fbarquez/pulsoxi_iot/images/Anexos/BPW34_Komponente.png

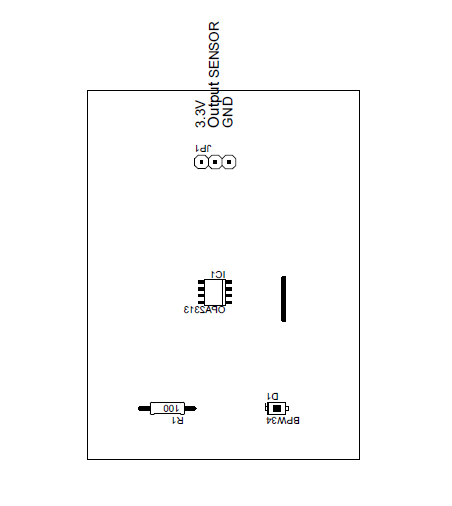
images/Anexos/BPW34_Komponente.png
