fbarquez/pulsoxi_iot/images/Anexos/BPW34_squema.png

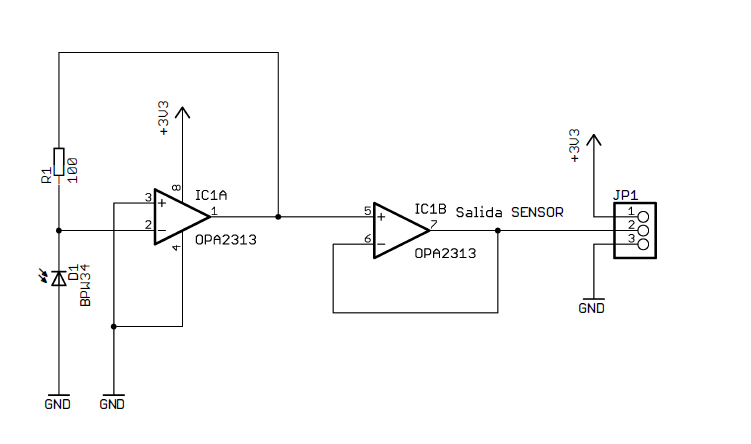
images/Anexos/BPW34_squema.png
