fbarquez/pulsoxi_iot/images/Anexos/IMG-20240221-WA0002.jpg

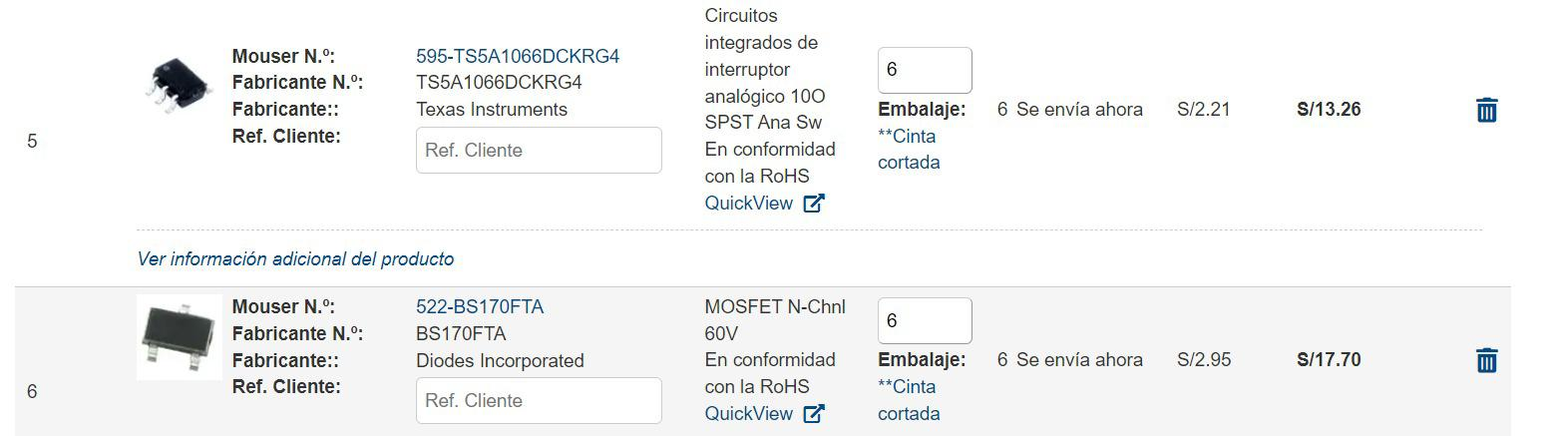
images/Anexos/IMG-20240221-WA0002.jpg
