fbarquez/pulsoxi_iot/images/Anexos/IMG-20240221-WA0005.jpg

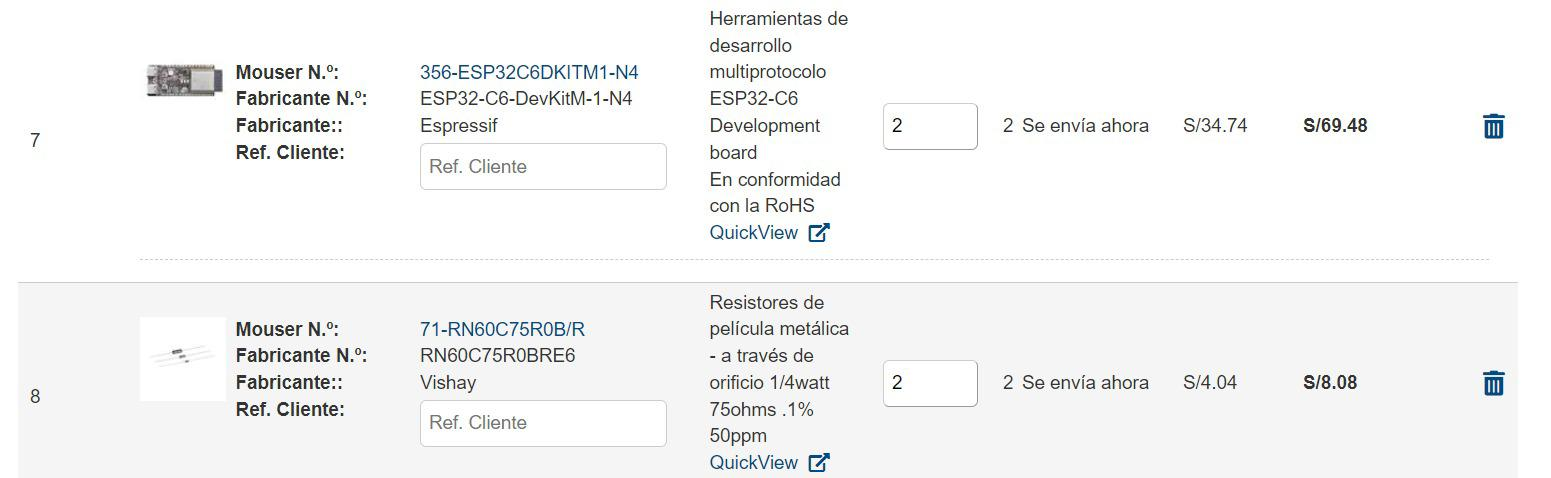
images/Anexos/IMG-20240221-WA0005.jpg
