fbarquez/pulsoxi_iot/images/Calculo Filtro pasabajos_y_filtro pasaaltos.png

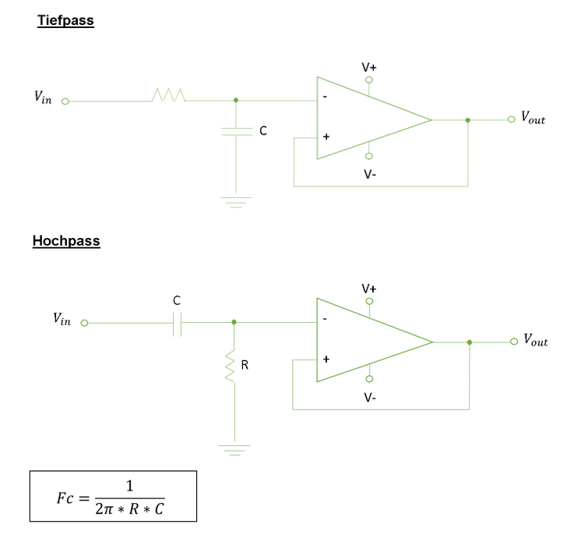
images/Calculo Filtro pasabajos_y_filtro pasaaltos.png
