fbarquez/pulsoxi_iot/images/Conexion_PIC16F1937_aESP32.jpg

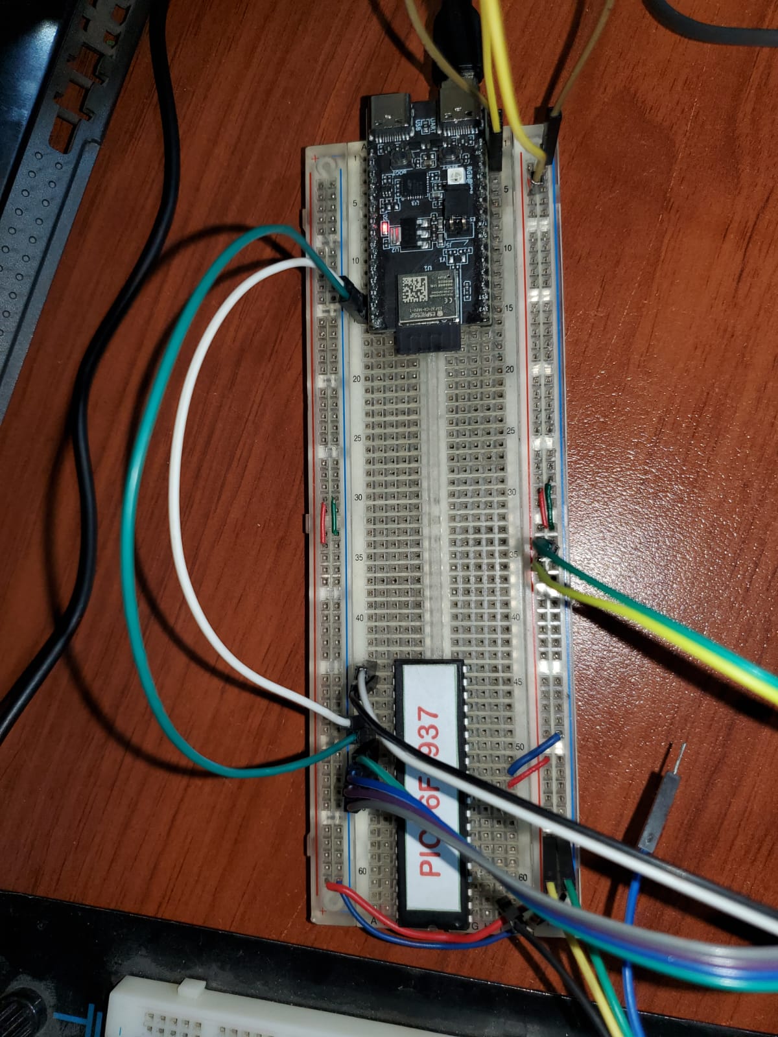
images/Conexion_PIC16F1937_aESP32.jpg
