fbarquez/pulsoxi_iot/images/Conexión PIC16F1937[6] misma Conexión.jpg

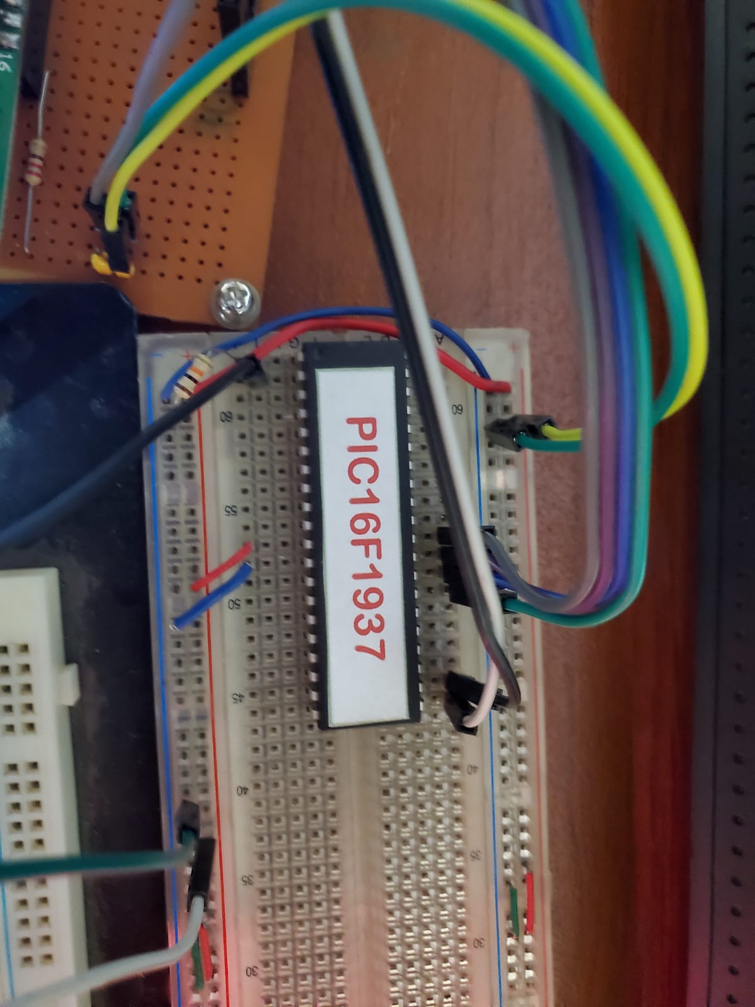
images/Conexión PIC16F1937[6] misma Conexión.jpg
