fbarquez/pulsoxi_iot/images/Cálculo amplificador no inversor.png

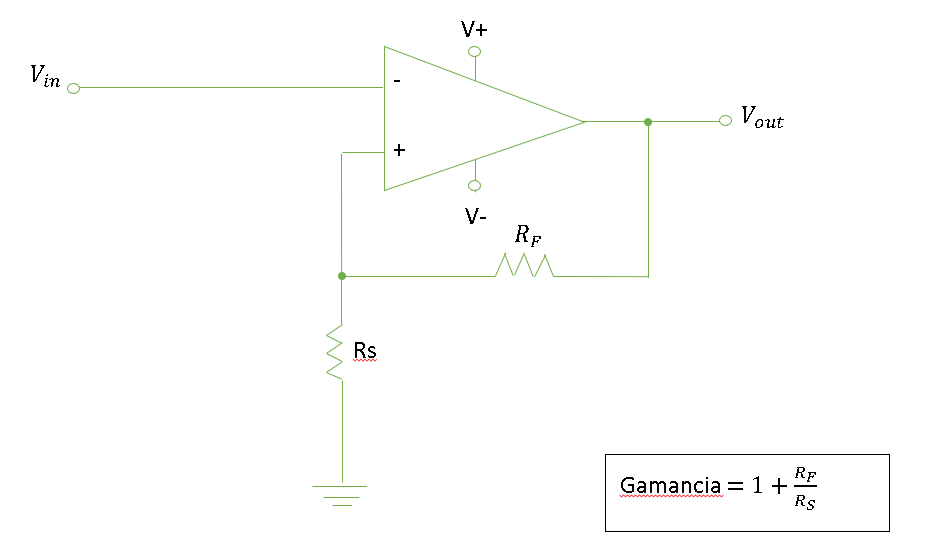
images/Cálculo amplificador no inversor.png
