fbarquez/pulsoxi_iot/images/Cálculo Conversor de corriente a Voltaje.png

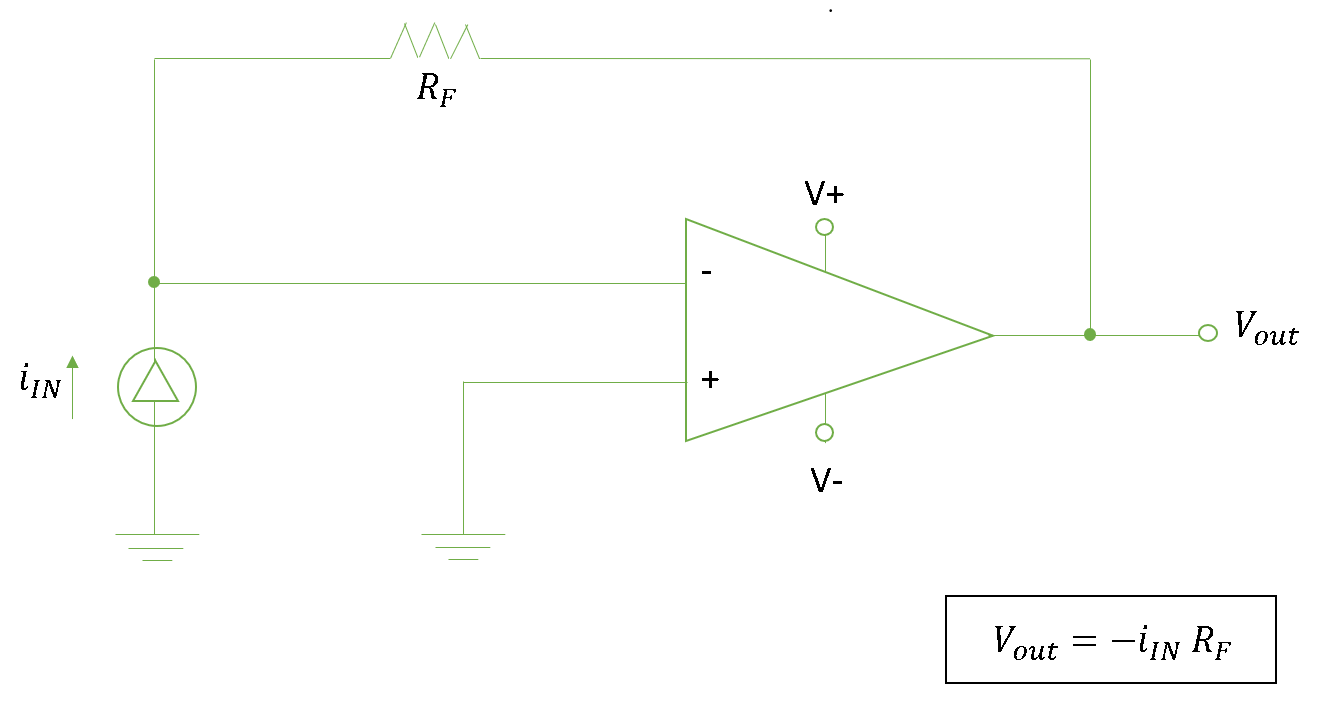
images/Cálculo Conversor de corriente a Voltaje.png
