fbarquez/pulsoxi_iot/images/DiagramadeConexion_SenhalesacondicionadasamicrocontroladoresPICyESP32.jpg

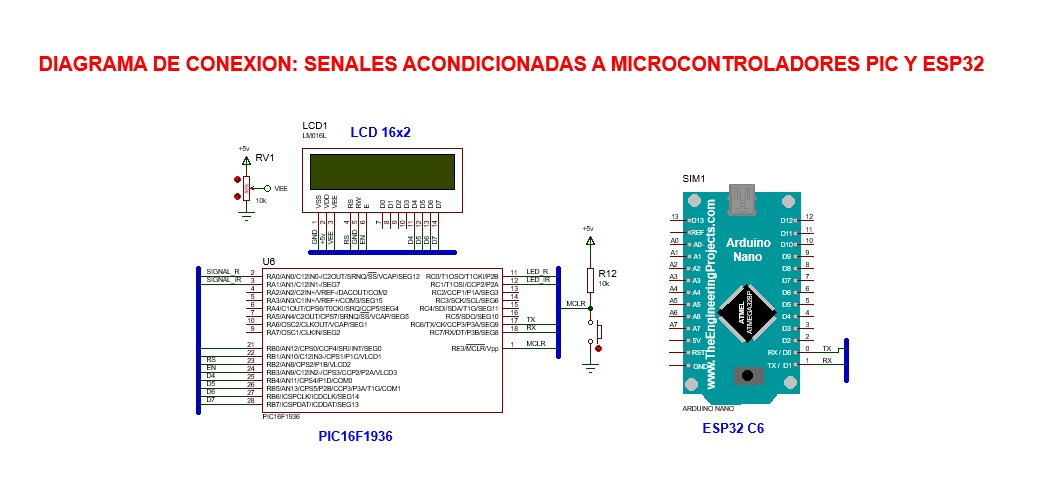
images/DiagramadeConexion_SenhalesacondicionadasamicrocontroladoresPICyESP32.jpg
