fbarquez/pulsoxi_iot/images/DiagramadeflujoparaelESP32.jpg

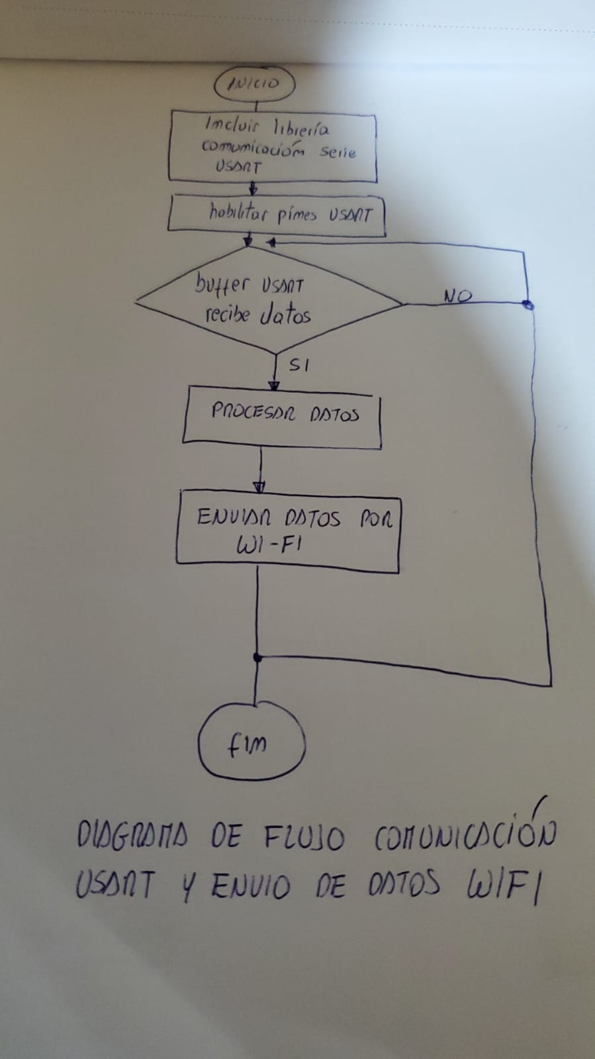
images/DiagramadeflujoparaelESP32.jpg
