fbarquez/pulsoxi_iot/images/Eagle/Board_Pulsoximeter.png

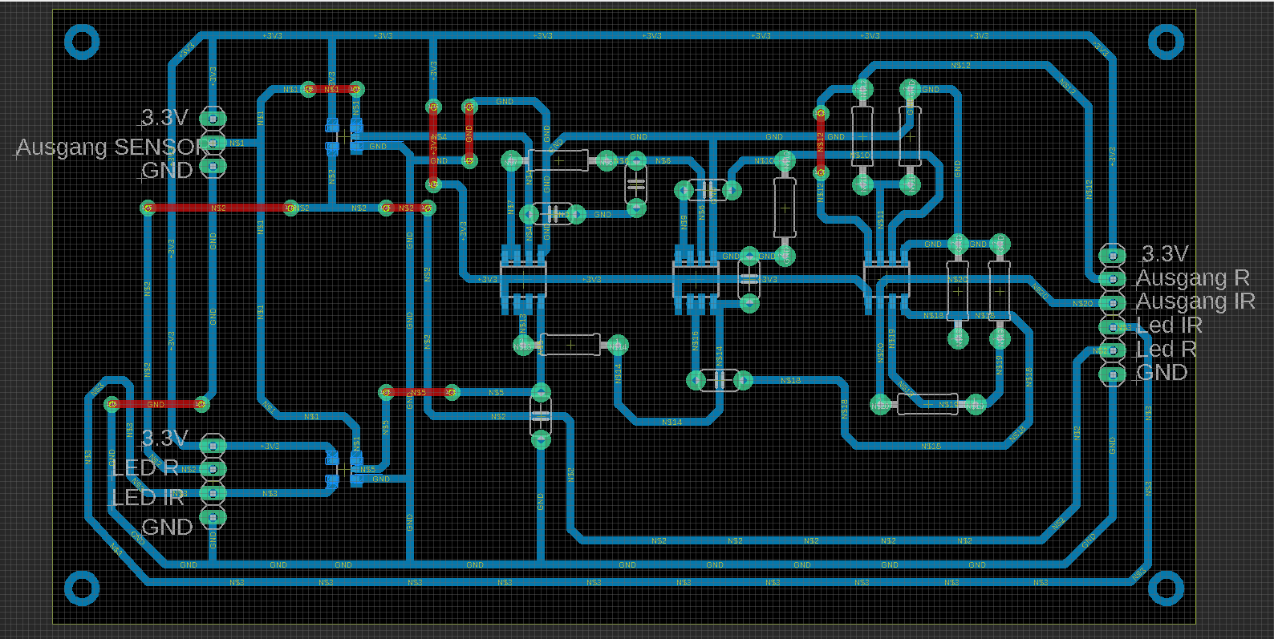
images/Eagle/Board_Pulsoximeter.png
