fbarquez/pulsoxi_iot/images/Eagle/Pulsioximeter_PCB_BottomSide.png

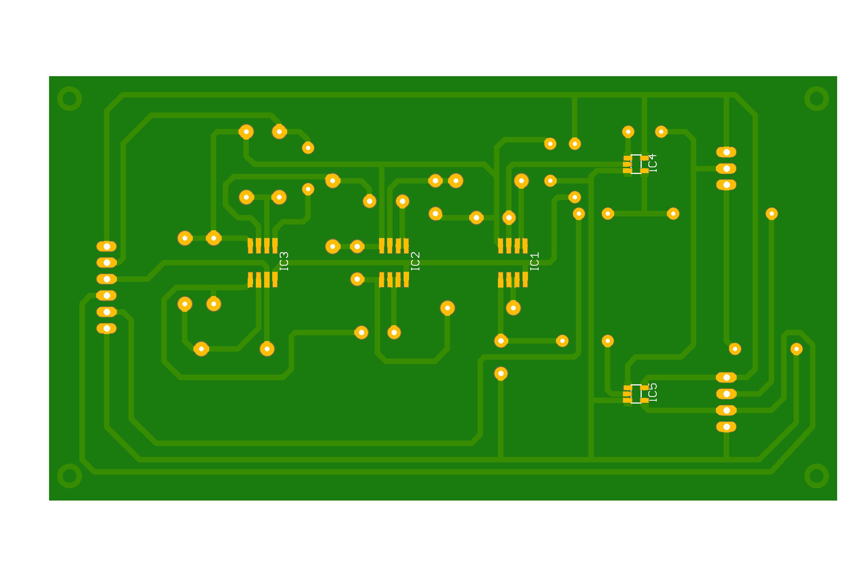
images/Eagle/Pulsioximeter_PCB_BottomSide.png
