fbarquez/pulsoxi_iot/images/Eagle/Pulsioximeter_PCB_TopSide.png

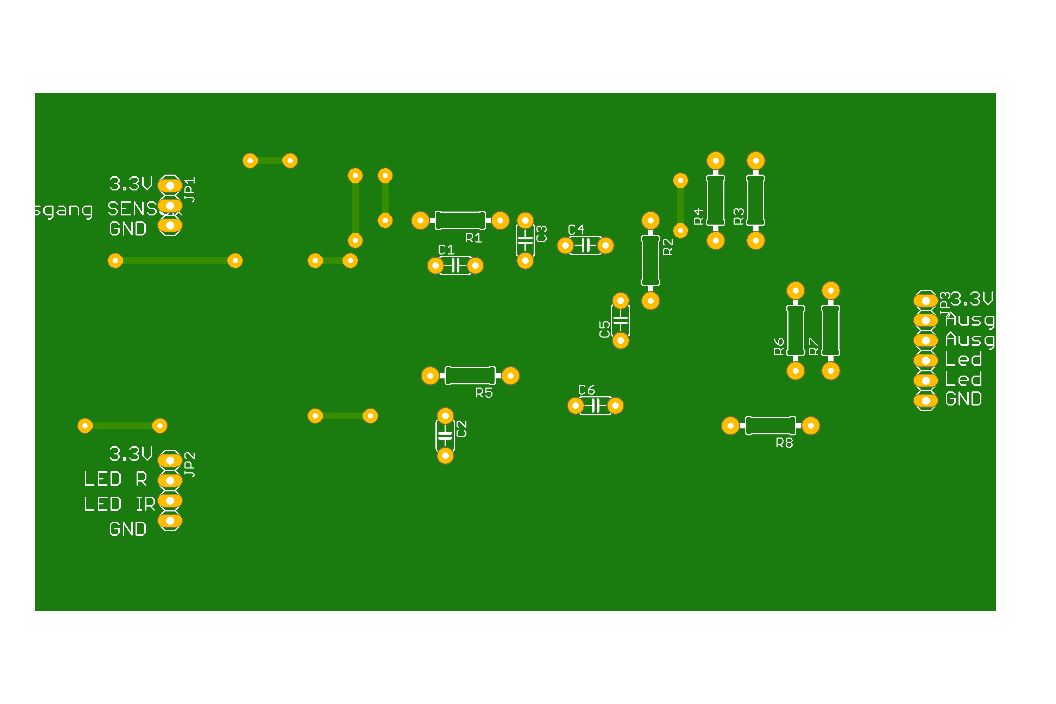
images/Eagle/Pulsioximeter_PCB_TopSide.png
