fbarquez/pulsoxi_iot/images/Eagle/Pulsioximetro_PCB_Drills.png

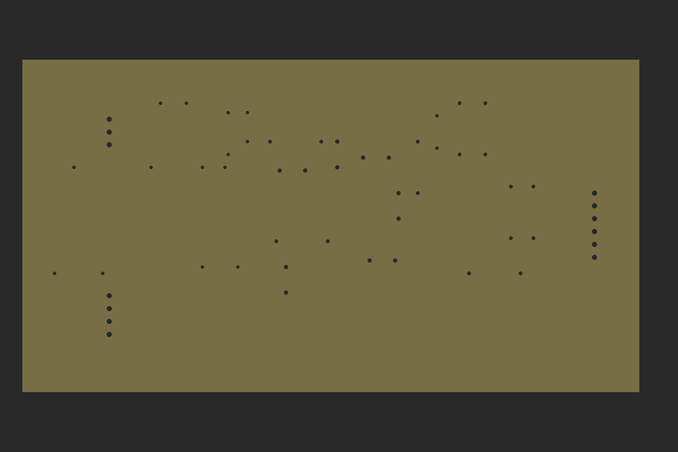
images/Eagle/Pulsioximetro_PCB_Drills.png
