fbarquez/pulsoxi_iot/images/Eagle/Schaltplan_BPW34.png

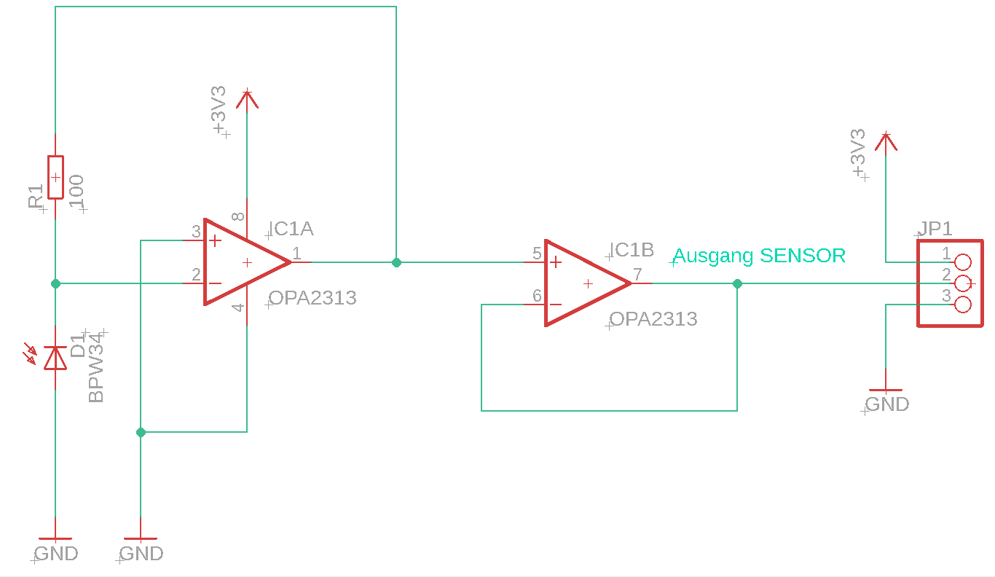
images/Eagle/Schaltplan_BPW34.png
