fbarquez/pulsoxi_iot/images/Eagle/Schaltplan_BS170.png

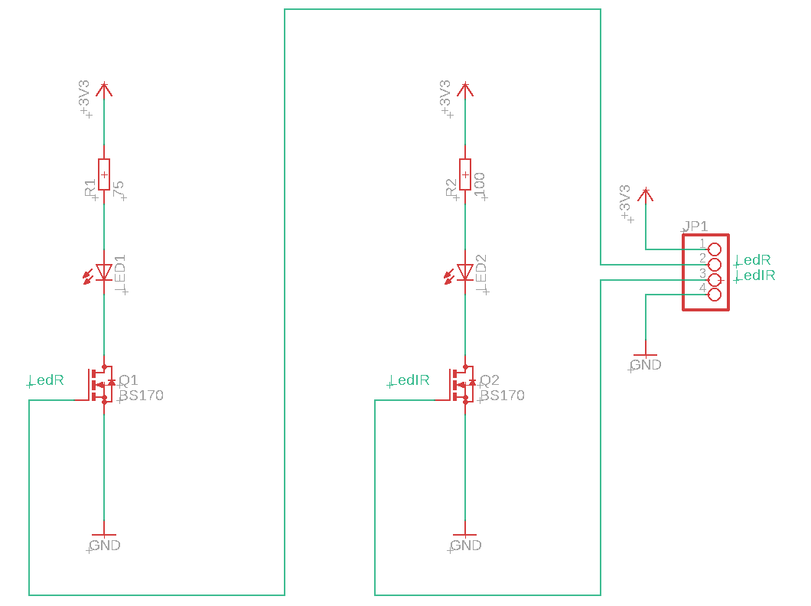
images/Eagle/Schaltplan_BS170.png
