fbarquez/pulsoxi_iot/images/Eagle/Schaltplan_Pulsoximeter.png

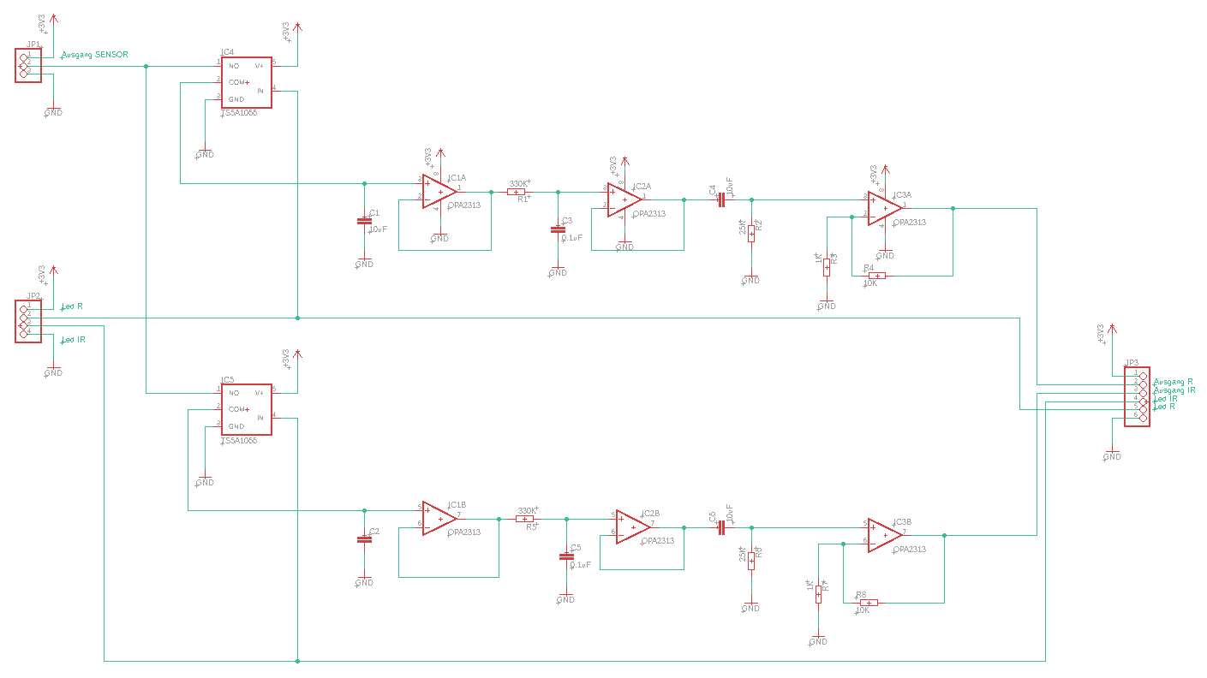
images/Eagle/Schaltplan_Pulsoximeter.png
