fbarquez/pulsoxi_iot/images/ESP32 C6.jpg

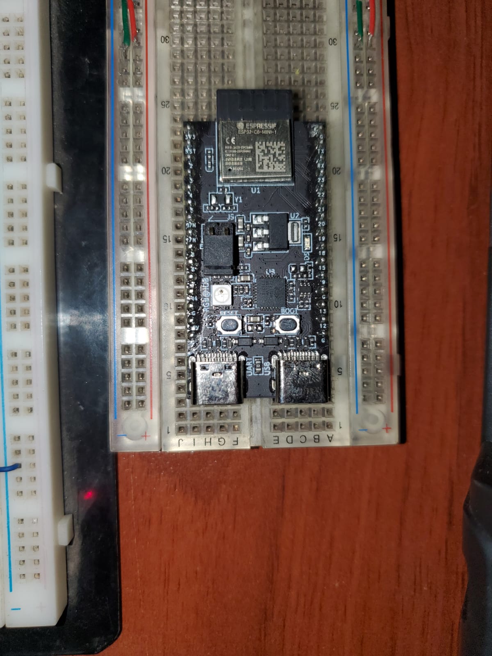
images/ESP32 C6.jpg
