fbarquez/pulsoxi_iot/images/Funcionamiento PIC16F_ESP32_Oximetro.jpg

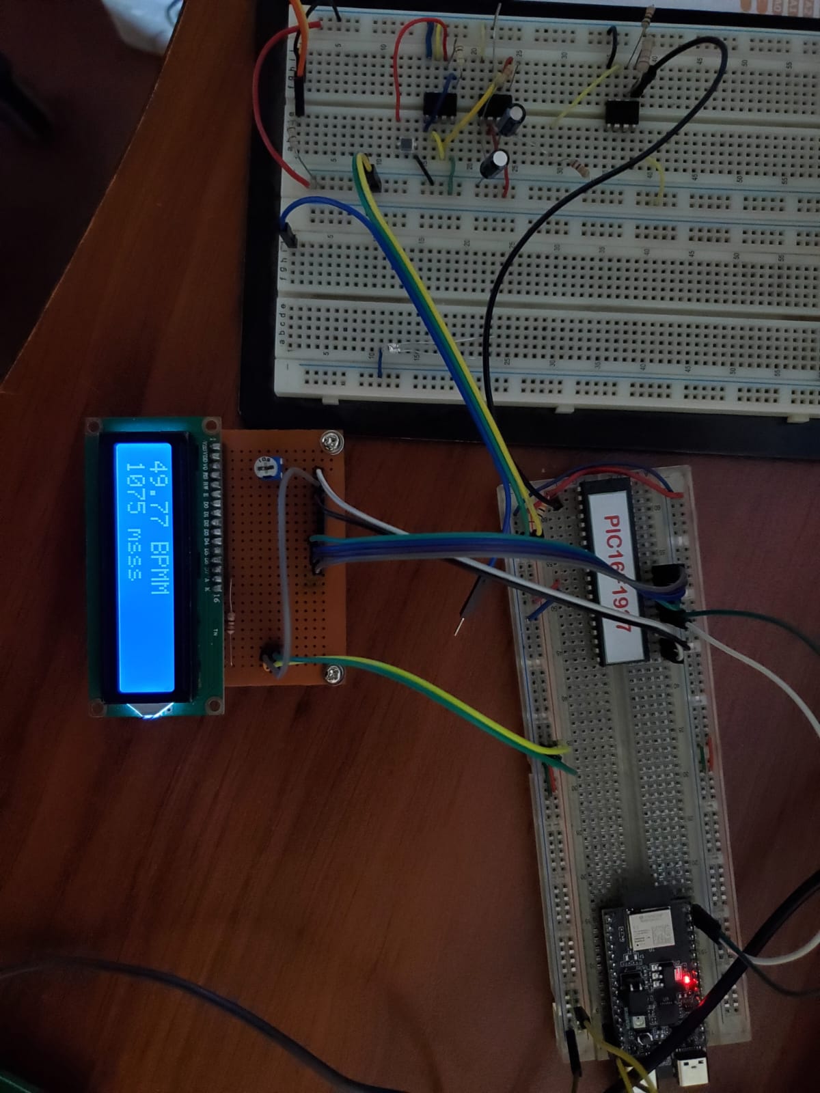
images/Funcionamiento PIC16F_ESP32_Oximetro.jpg
