fbarquez/pulsoxi_iot/images/Gesetz von Lambert-Beer.png

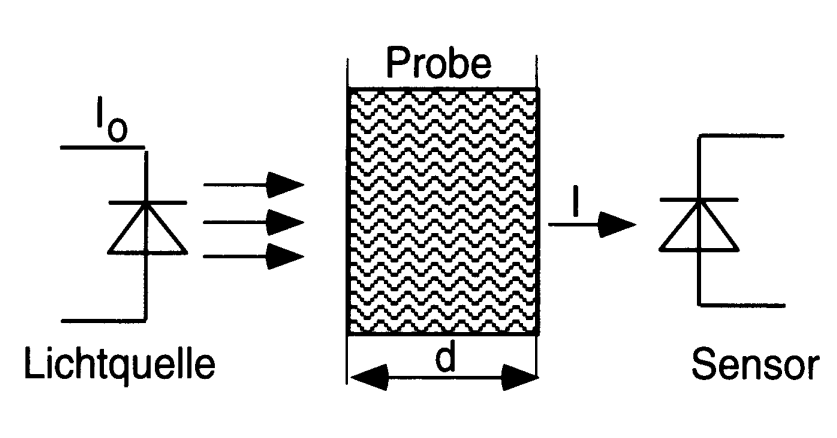
images/Gesetz von Lambert-Beer.png
