fbarquez/pulsoxi_iot/images/Infrarot_abmessungen.png

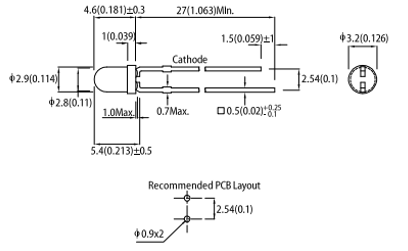
images/Infrarot_abmessungen.png
