fbarquez/pulsoxi_iot/images/Infrarot_relativeintensitaet_vs_wellenlaenge.png

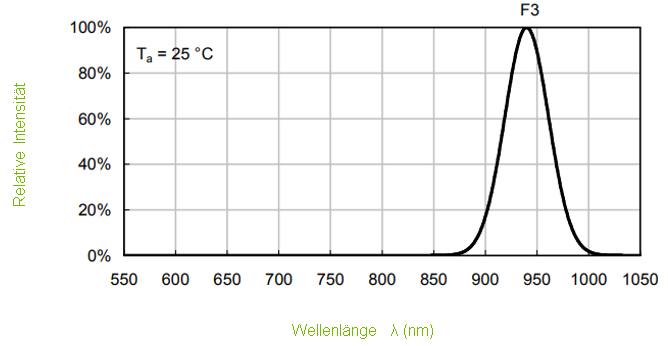
images/Infrarot_relativeintensitaet_vs_wellenlaenge.png
