fbarquez/pulsoxi_iot/images/Investigacion/Screenshot 2024-02-20 182740.png

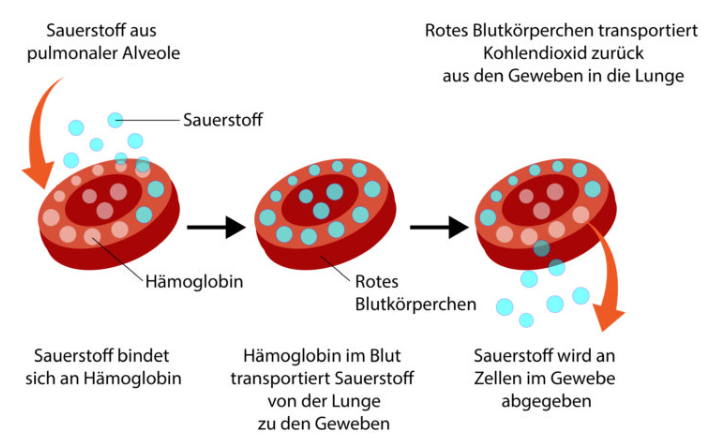
images/Investigacion/Screenshot 2024-02-20 182740.png
