fbarquez/pulsoxi_iot/images/LCD - Mostrando Frecuencia Cardíaca.jpg

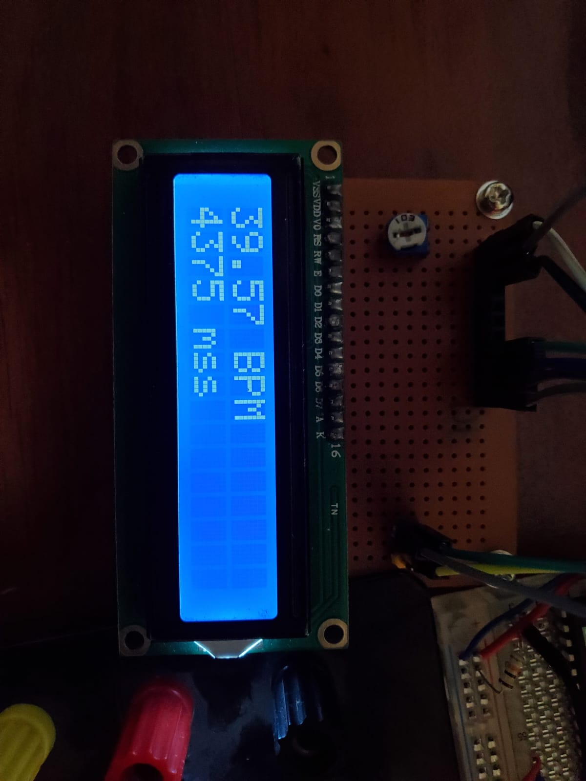
images/LCD - Mostrando Frecuencia Cardíaca.jpg
