fbarquez/pulsoxi_iot/images/LED_abmessungen.png

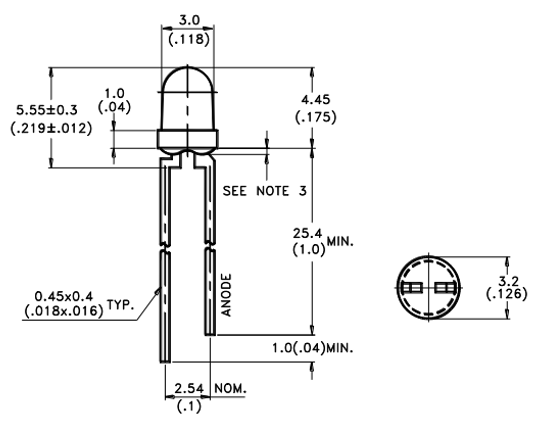
images/LED_abmessungen.png
