fbarquez/pulsoxi_iot/images/LED_relativeintensitaet_vs_wellenlaenge.png

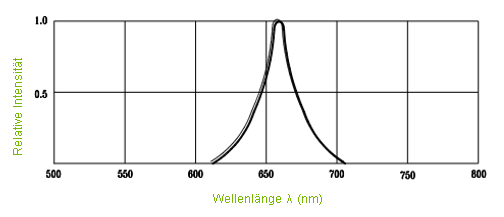
images/LED_relativeintensitaet_vs_wellenlaenge.png
