fbarquez/pulsoxi_iot/images/PAP_1.png

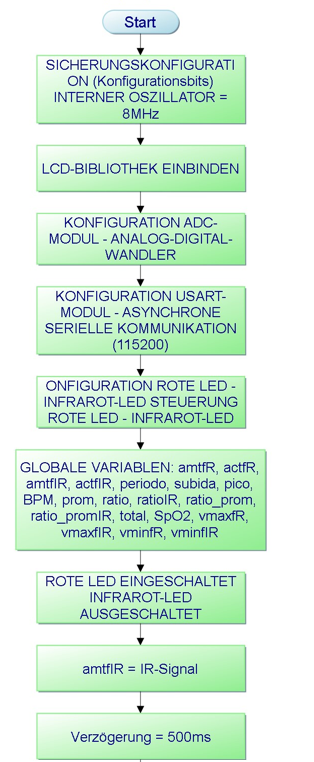
images/PAP_1.png
