fbarquez/pulsoxi_iot/images/PAP_2.png

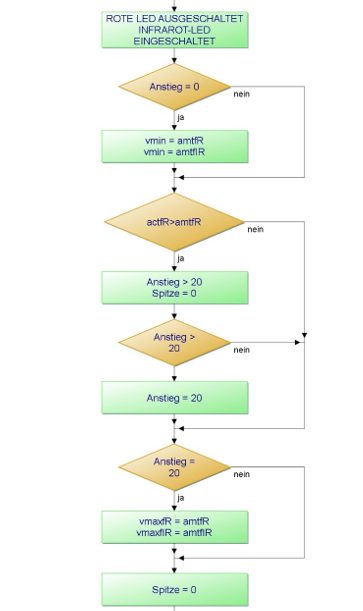
images/PAP_2.png
