fbarquez/pulsoxi_iot/images/PAP_3.png

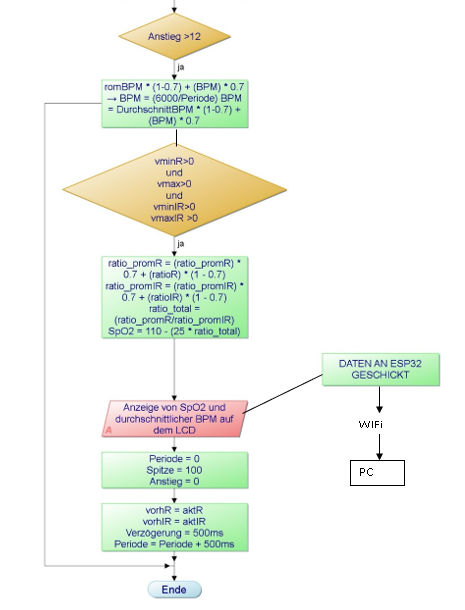
images/PAP_3.png
