fbarquez/pulsoxi_iot/images/PCB/Acodicionamiento_PCB_elaboracionpropia.jpg

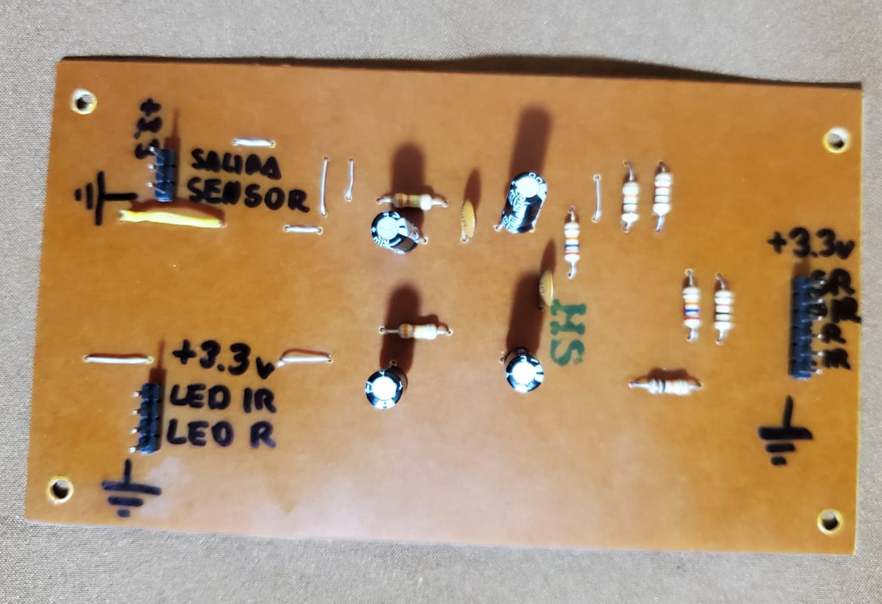
images/PCB/Acodicionamiento_PCB_elaboracionpropia.jpg
