fbarquez/pulsoxi_iot/images/PCB/EmisorOptico_PCB_elaboracionpropia.jpg

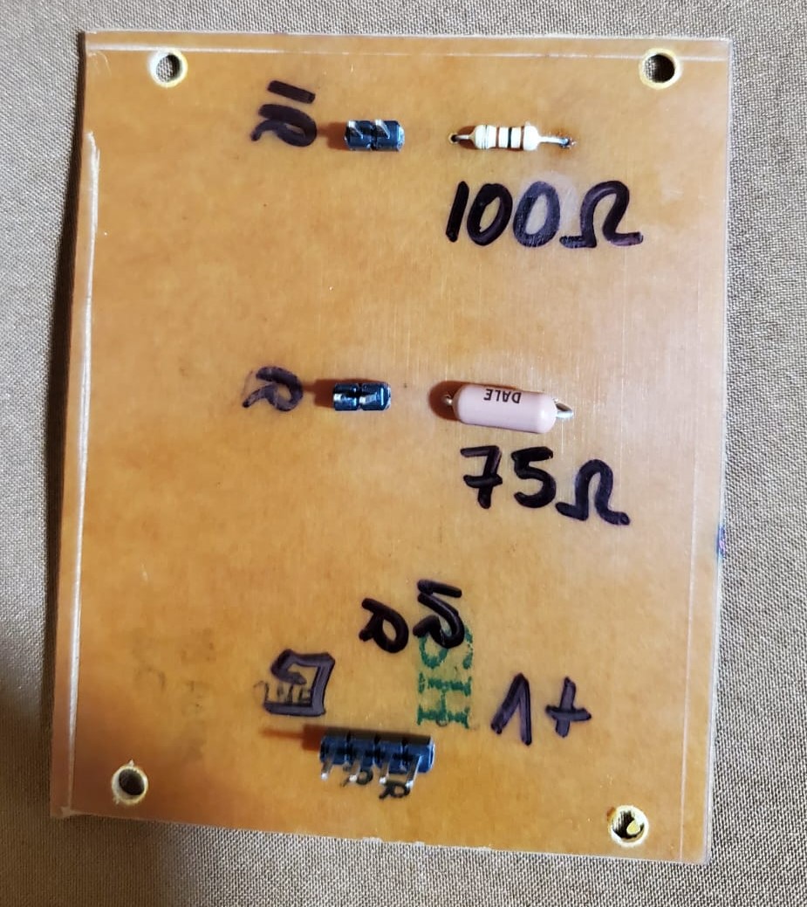
images/PCB/EmisorOptico_PCB_elaboracionpropia.jpg
