fbarquez/pulsoxi_iot/images/PCB/EmisorOptico_PCB_elaboracionpropia_2.jpg

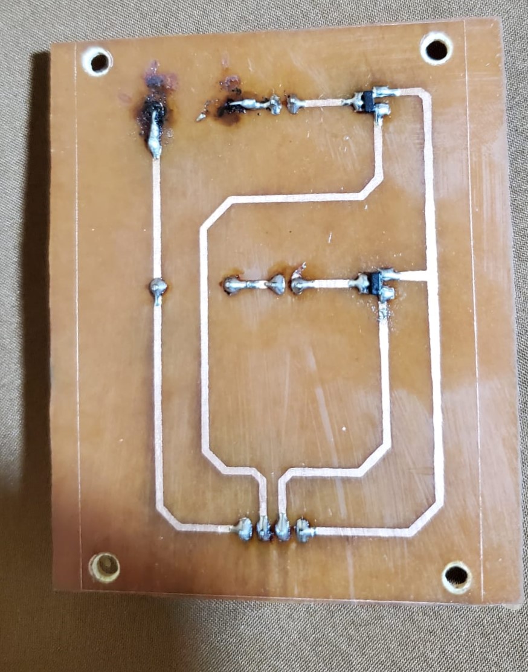
images/PCB/EmisorOptico_PCB_elaboracionpropia_2.jpg
