fbarquez/pulsoxi_iot/images/PCB/PCB_acondicionamiento_d_ señales_Buffer __Filtrospasaaltos_y _bajos__amplificador.jpg

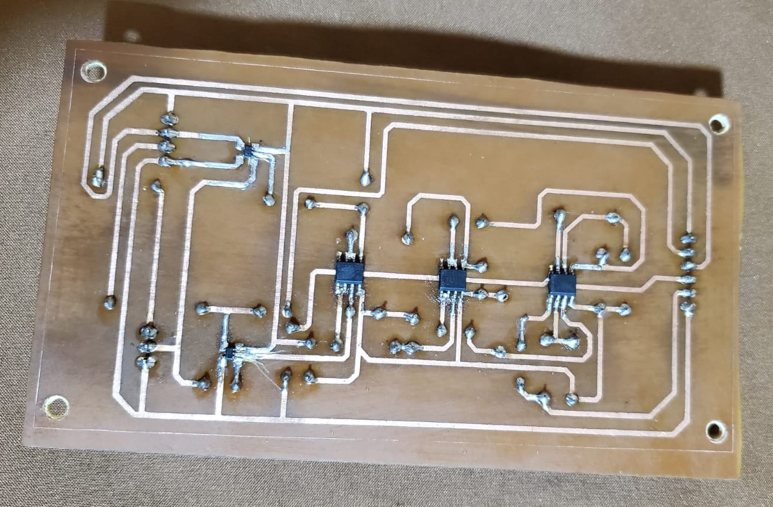
images/PCB/PCB_acondicionamiento_d_ señales_Buffer __Filtrospasaaltos_y _bajos__amplificador.jpg
