fbarquez/pulsoxi_iot/images/PCB/Prototipo_en_Protoboard.jpg

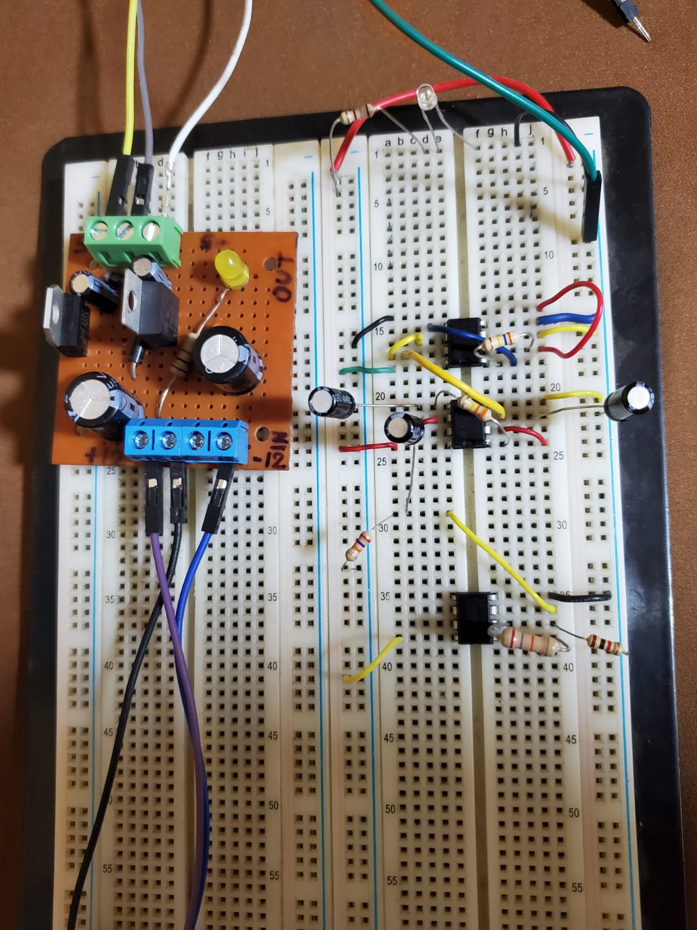
images/PCB/Prototipo_en_Protoboard.jpg
