fbarquez/pulsoxi_iot/images/PCB/Screenshot 2024-02-18 211945.png

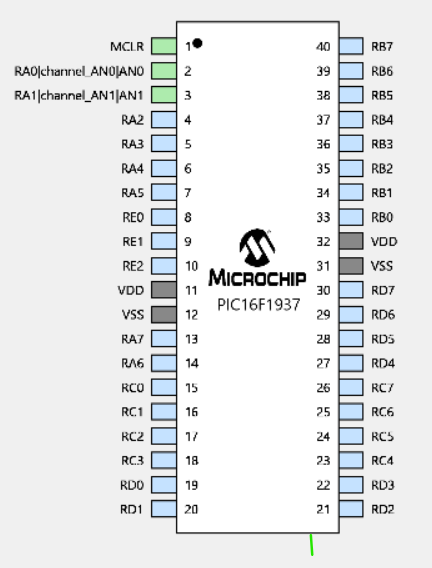
images/PCB/Screenshot 2024-02-18 211945.png
