fbarquez/pulsoxi_iot/images/Programm/SystemModule_KonfigurationinMplab.png

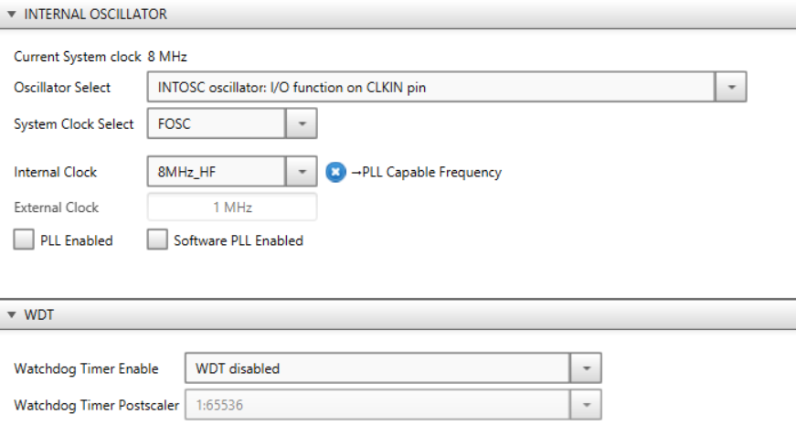
images/Programm/SystemModule_KonfigurationinMplab.png
