fbarquez/pulsoxi_iot/images/Programmablaufplan_Pulsoximeter.png

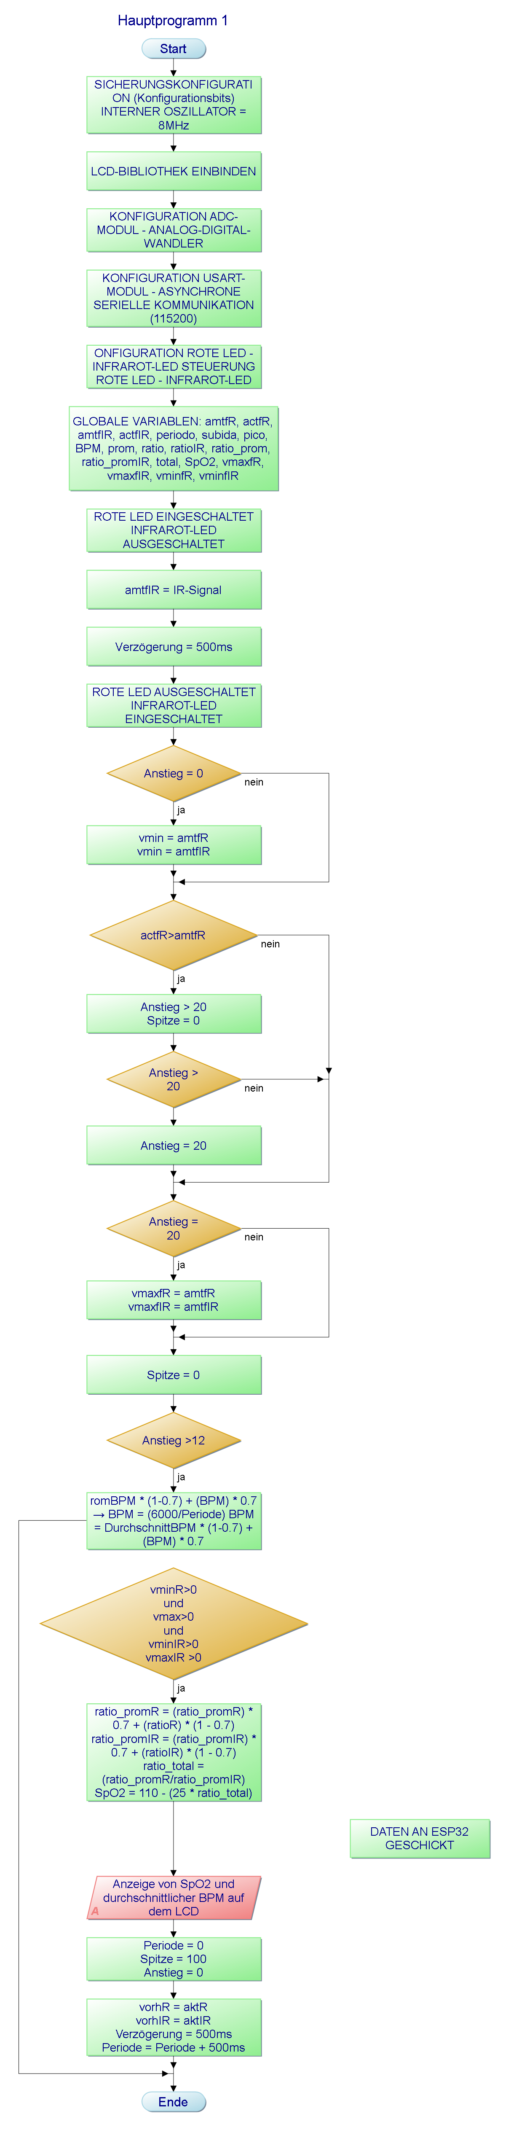
images/Programmablaufplan_Pulsoximeter.png
