fbarquez/pulsoxi_iot/images/Proteus/EmittirendeLeds.png

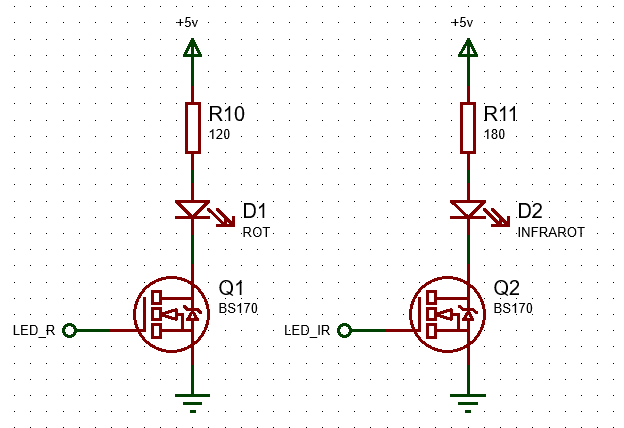
images/Proteus/EmittirendeLeds.png
