fbarquez/pulsoxi_iot/images/Proteus/FiltirungVerstaerker.png

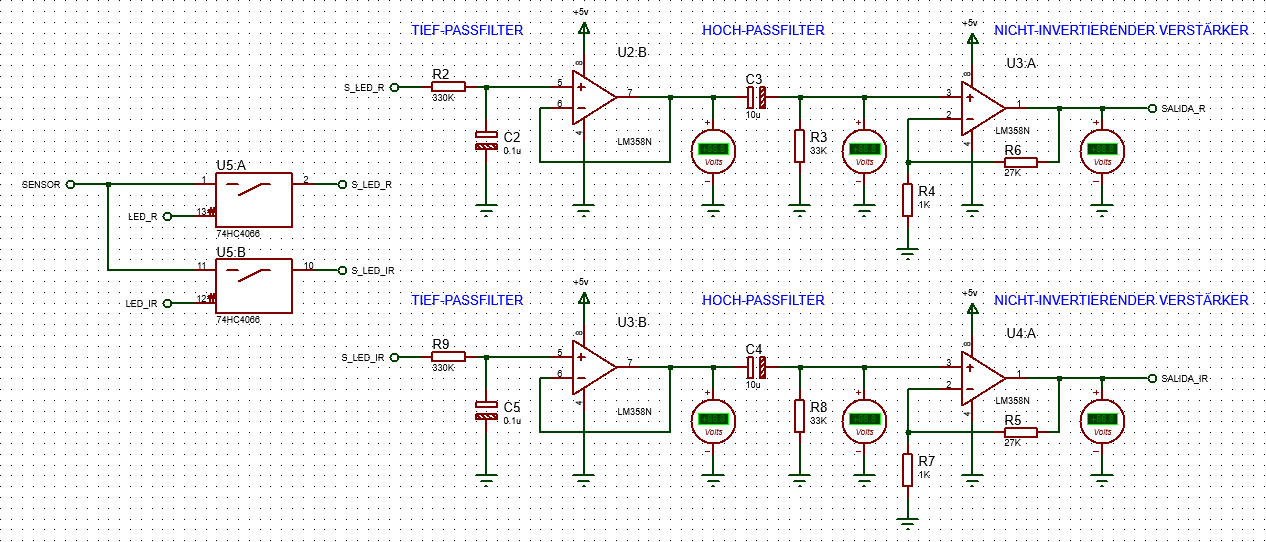
images/Proteus/FiltirungVerstaerker.png
