fbarquez/pulsoxi_iot/images/Proteus/OptischerSensor.png

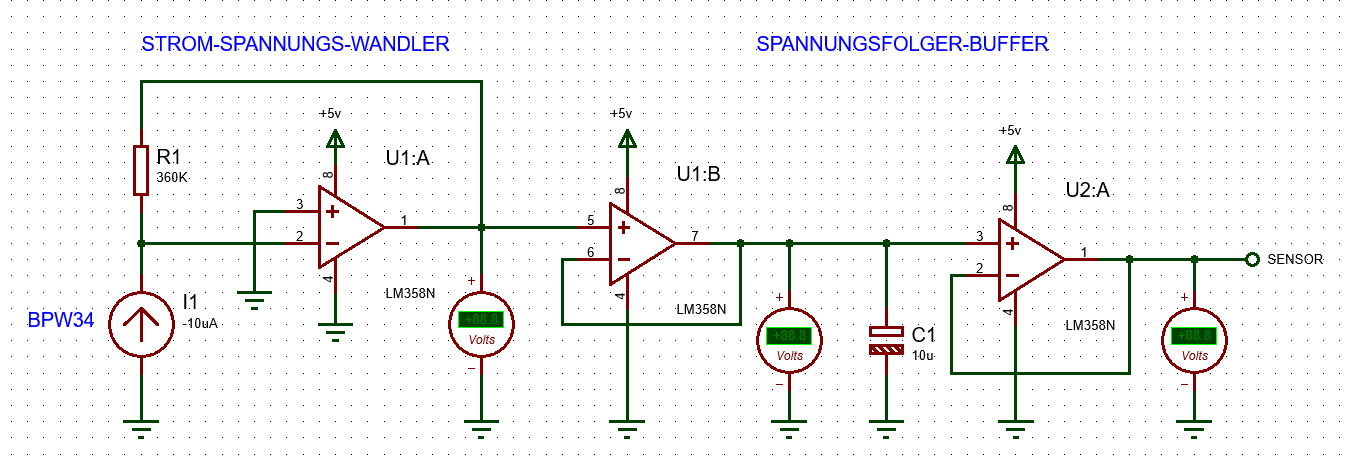
images/Proteus/OptischerSensor.png
