fbarquez/pulsoxi_iot/images/Proteus/VERBINDUNGSDIAGRAMM_VORBEREITETESIGNALEZUPICUNDESP32MIKROCONTROLLERN.png

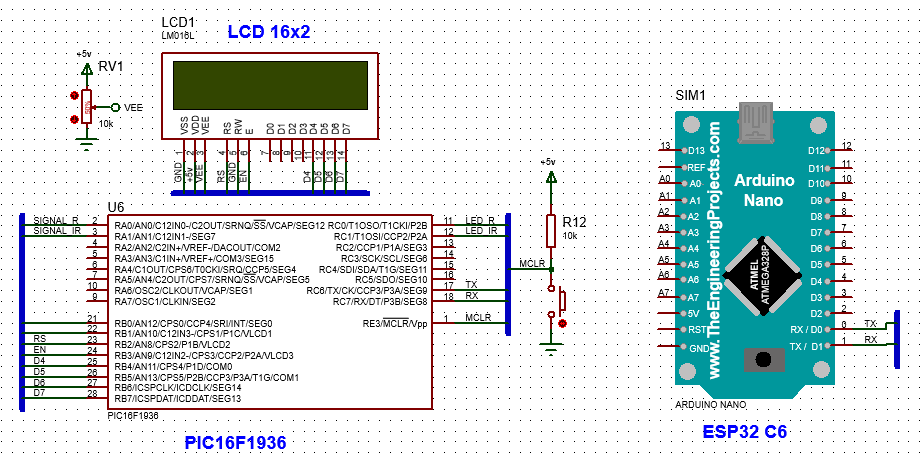
images/Proteus/VERBINDUNGSDIAGRAMM_VORBEREITETESIGNALEZUPICUNDESP32MIKROCONTROLLERN.png
