fbarquez/pulsoxi_iot/images/Screenshot 2024-02-19 161204.png

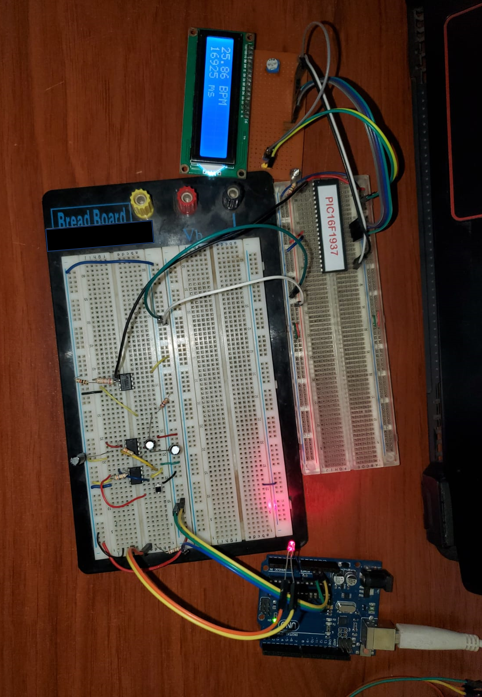
images/Screenshot 2024-02-19 161204.png
