fbarquez/pulsoxi_iot/images/Thingspeak.jpg

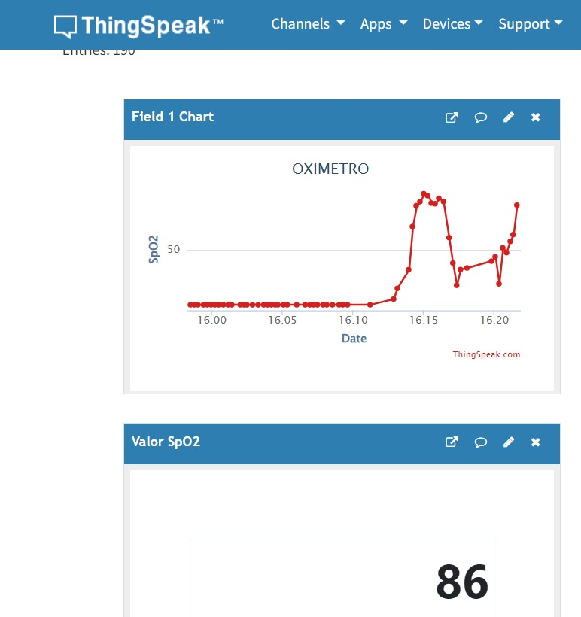
images/Thingspeak.jpg
