fbarquez/pulsoxi_iot/images/thingspeak_2.jpg

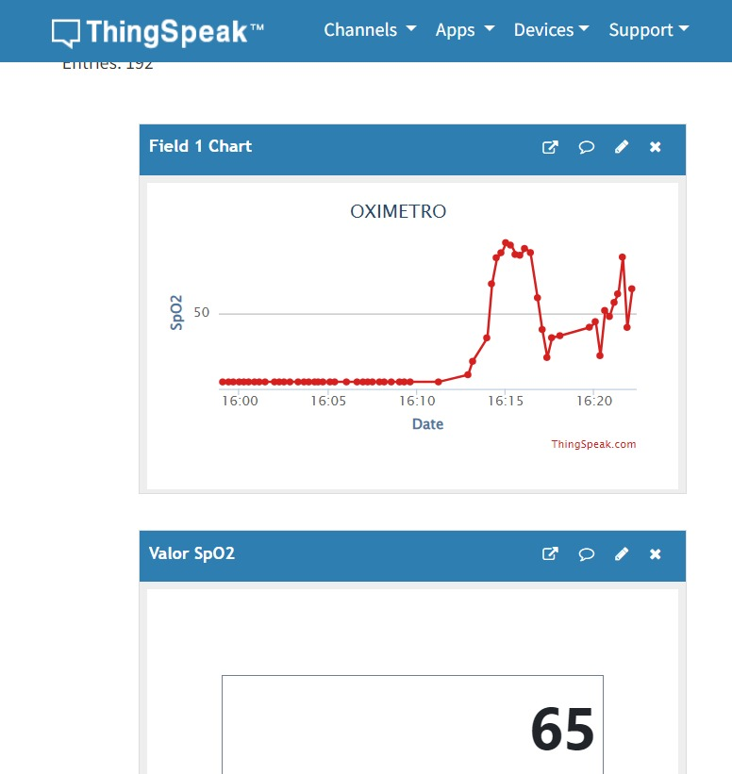
images/thingspeak_2.jpg
