fbarquez/pulsoxi_iot/images/thingspeak_3.jpg

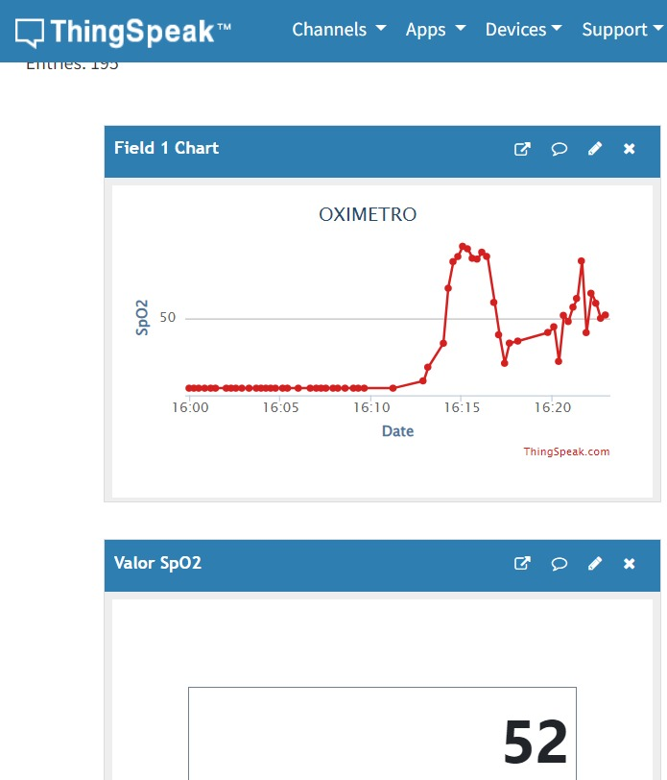
images/thingspeak_3.jpg
