fbarquez/pulsoxi_iot/images/USART-Kommunikation und WiFi-Datenübertragung.png

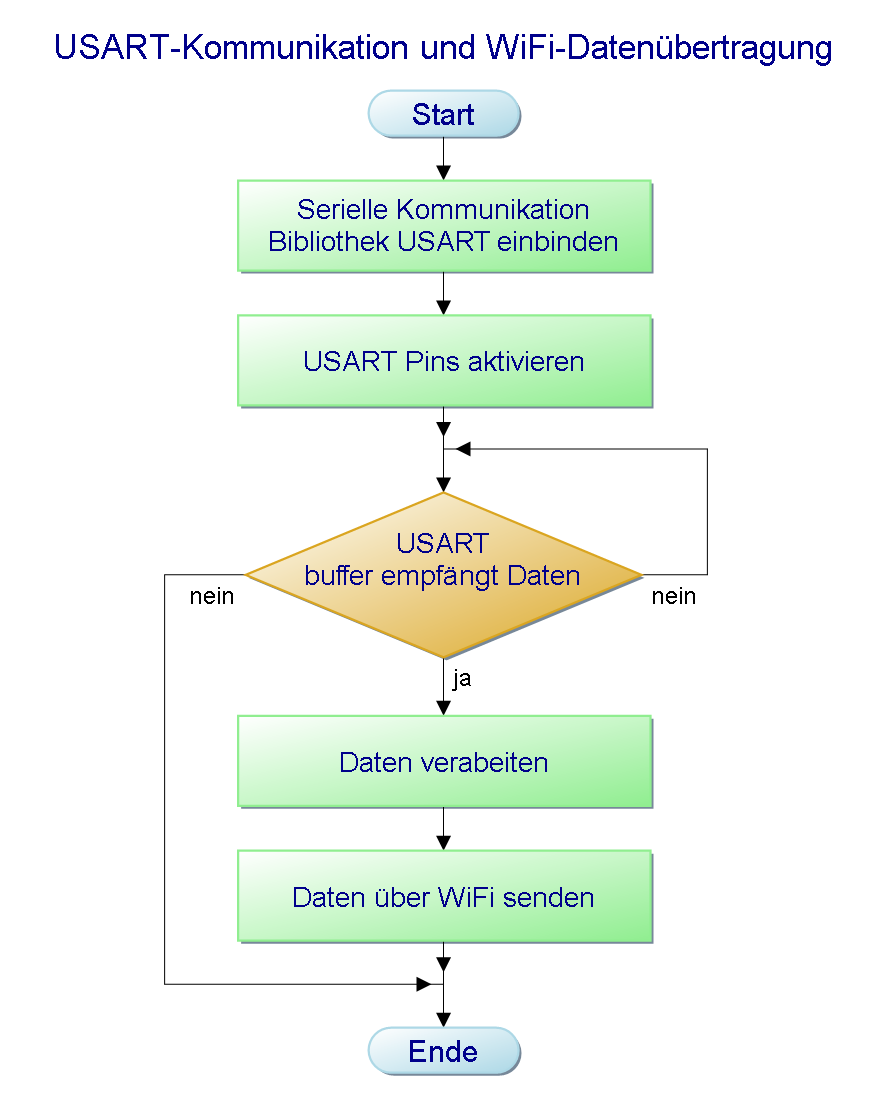
images/USART-Kommunikation und WiFi-Datenübertragung.png
