fbarquez/pulsoxi_iot/images/Prueba led inflarojo y receptor óptico.jpg

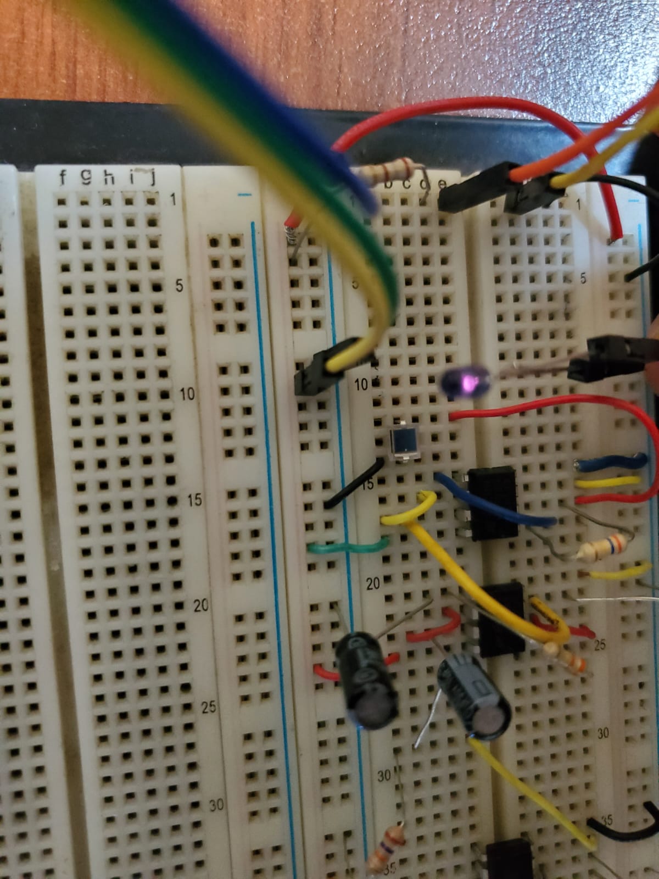
images/Prueba led inflarojo y receptor óptico.jpg
