fbarquez/pulsoxi_iot/images/Prueba Led rojo y receptor Optico.jpg

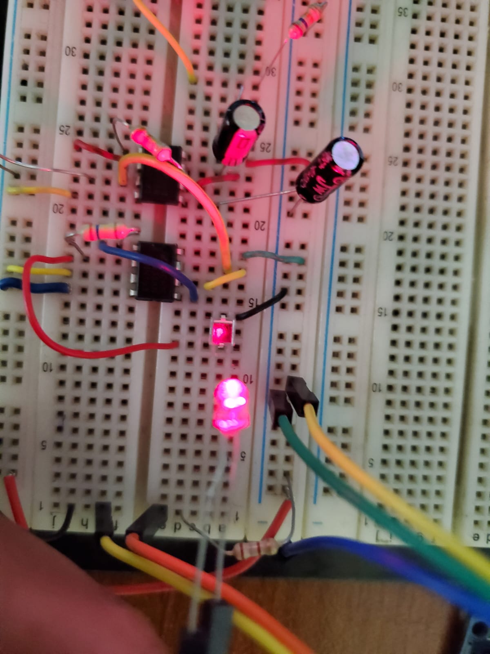
images/Prueba Led rojo y receptor Optico.jpg
