fbarquez/pulsoxi_iot/images/pruebadequetodofunciona_2.jpg

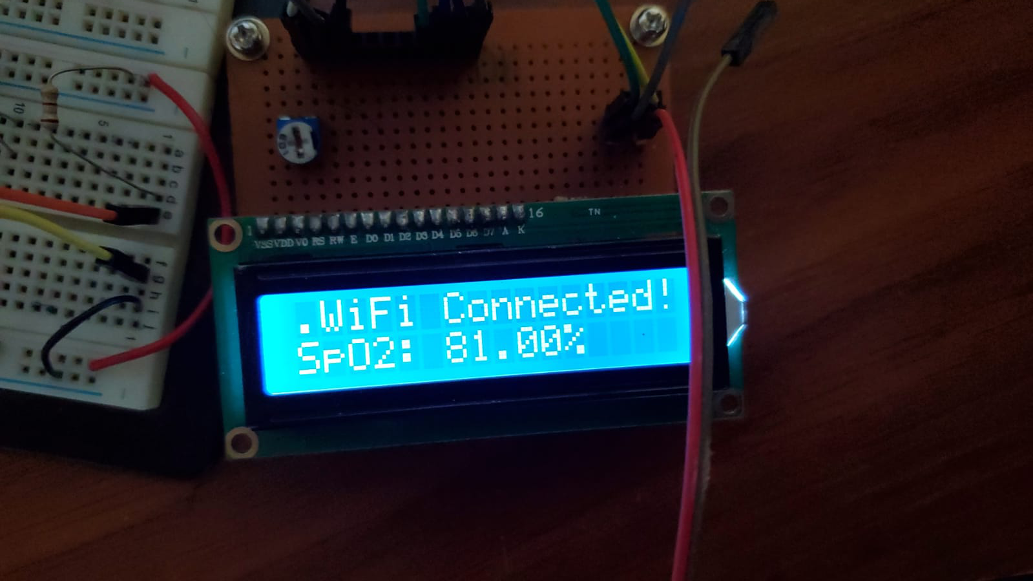
images/pruebadequetodofunciona_2.jpg
