fbarquez/pulsoxi_iot/images/resultado final_thingspeak.jpg

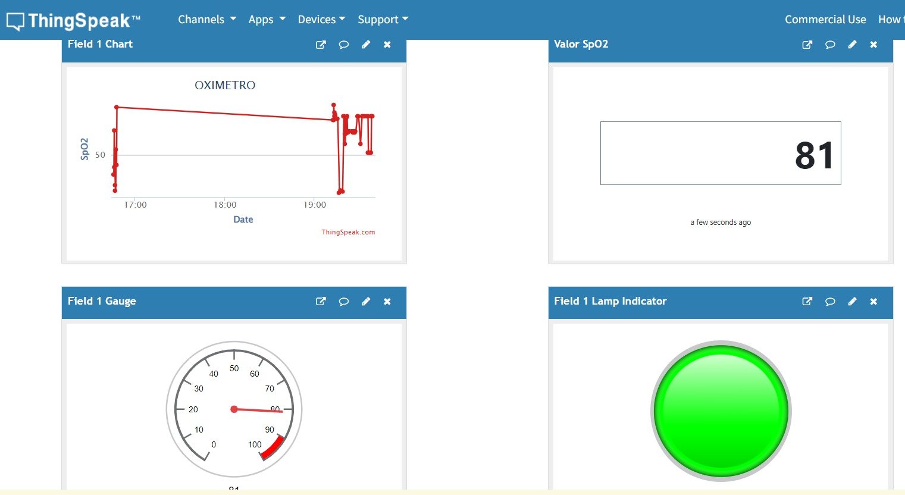
images/resultado final_thingspeak.jpg
